m24h/picburner/hardware/output/picburner_pcb.png

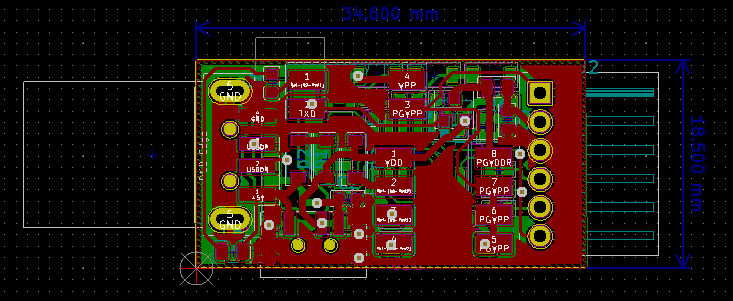
hardware/output/picburner_pcb.png
