m24h/picburner/hardware/output/picburner_sch.png

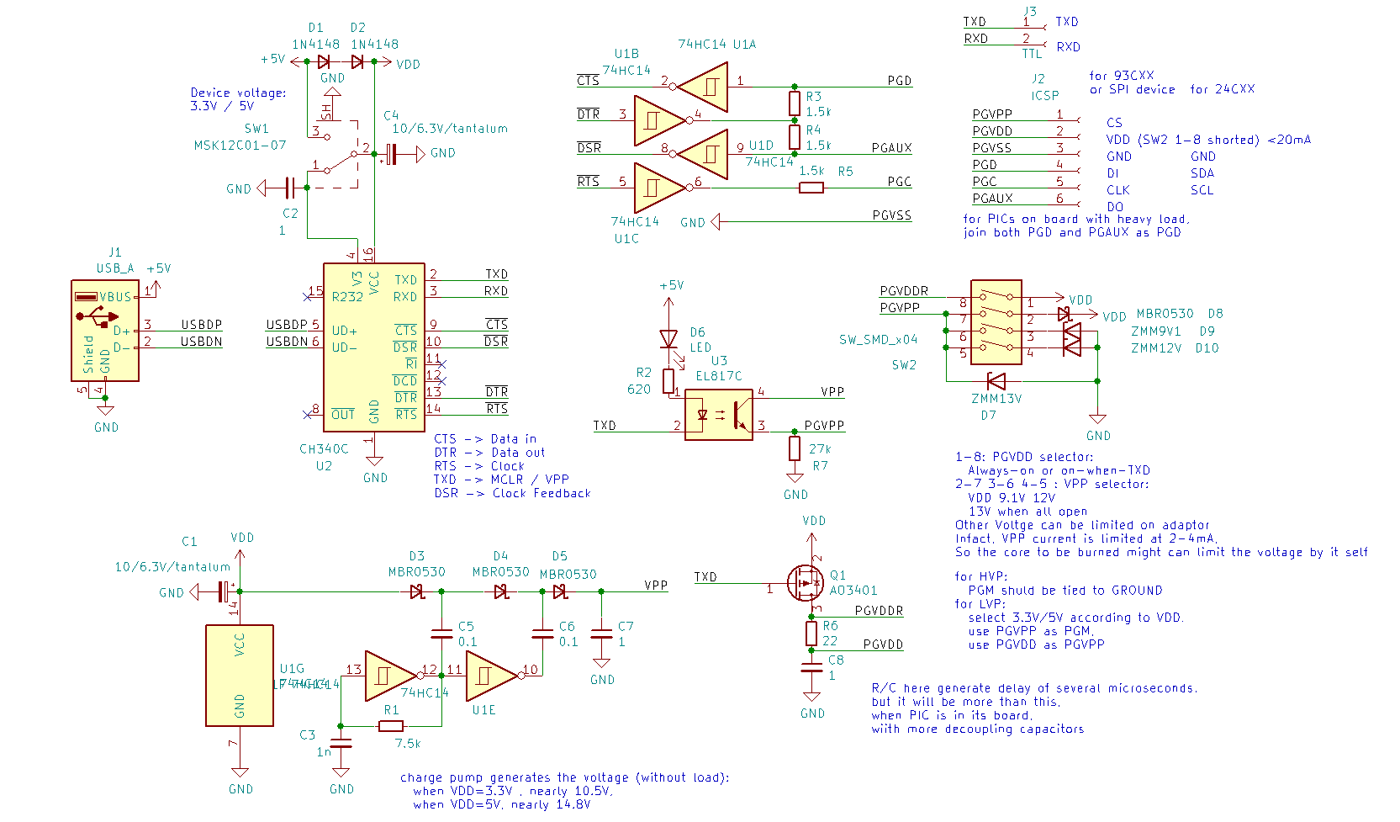
hardware/output/picburner_sch.png
